rayray2002/TPE-2014/3D/635612493688338750.jpg

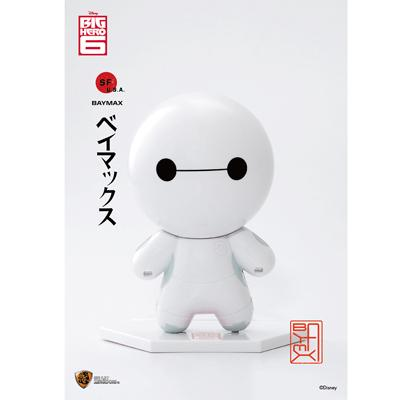
3D/635612493688338750.jpg
