rayray2002/TPE-2014/3D/doggie/images/doggie_front.jpg

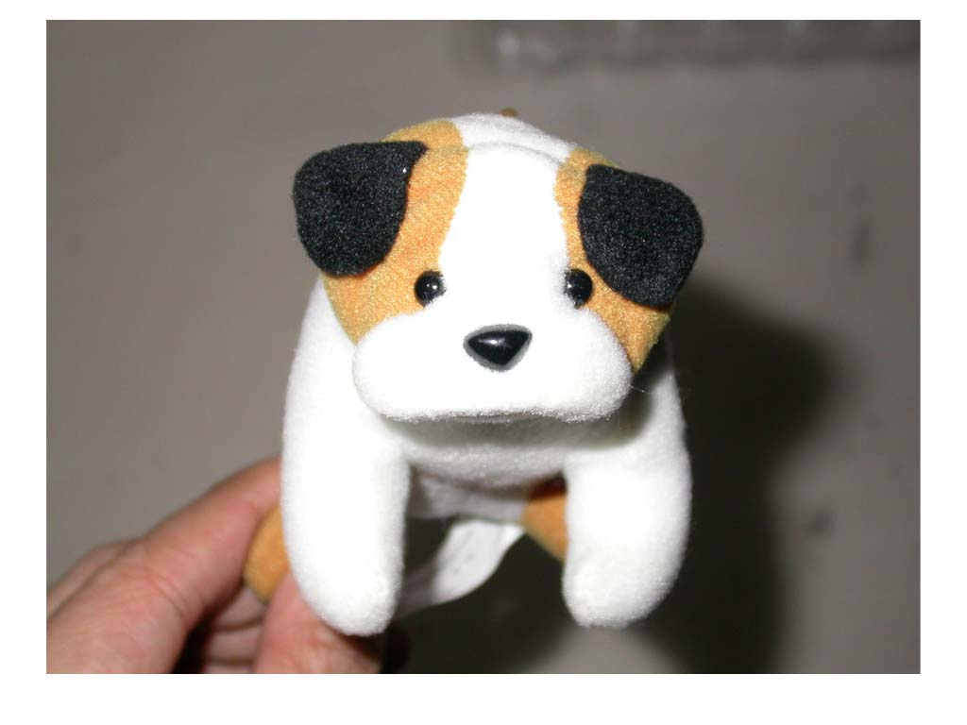
3D/doggie/images/doggie_front.jpg
