rayray2002/TPE-2014/document/Deep Sea Submarine.png

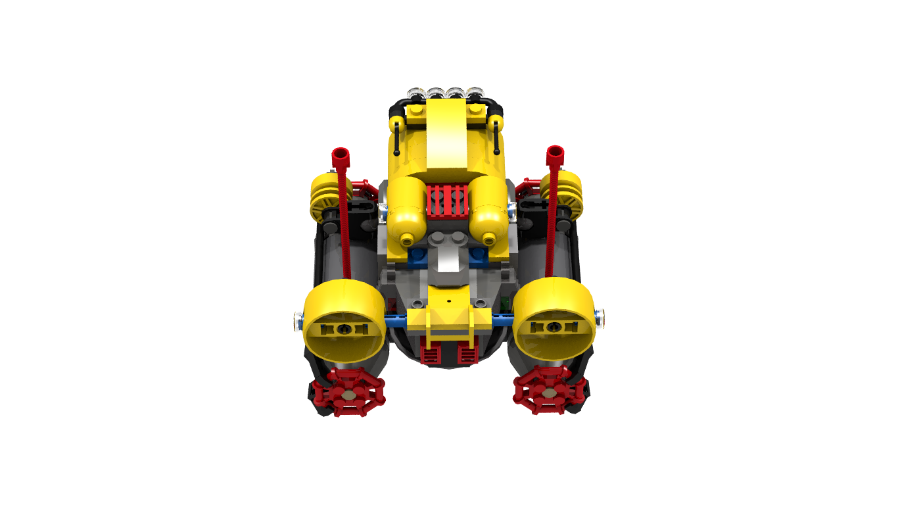
document/Deep Sea Submarine.png
