rayray2002/TPE-2014/document/images/20ms.png

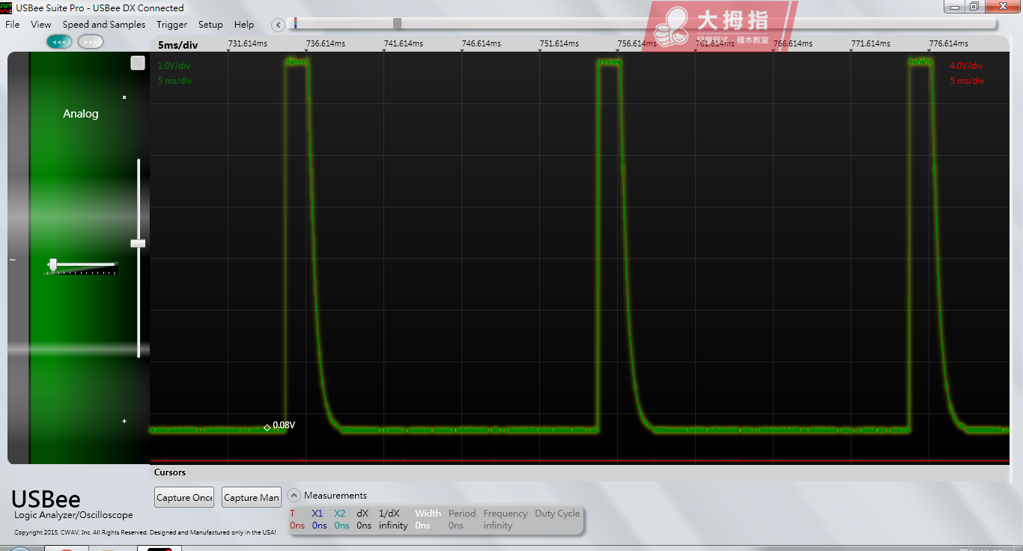
document/images/20ms.png
