rayray2002/TPE-2014/document/images/.picasaoriginals/IMG_7483.JPG

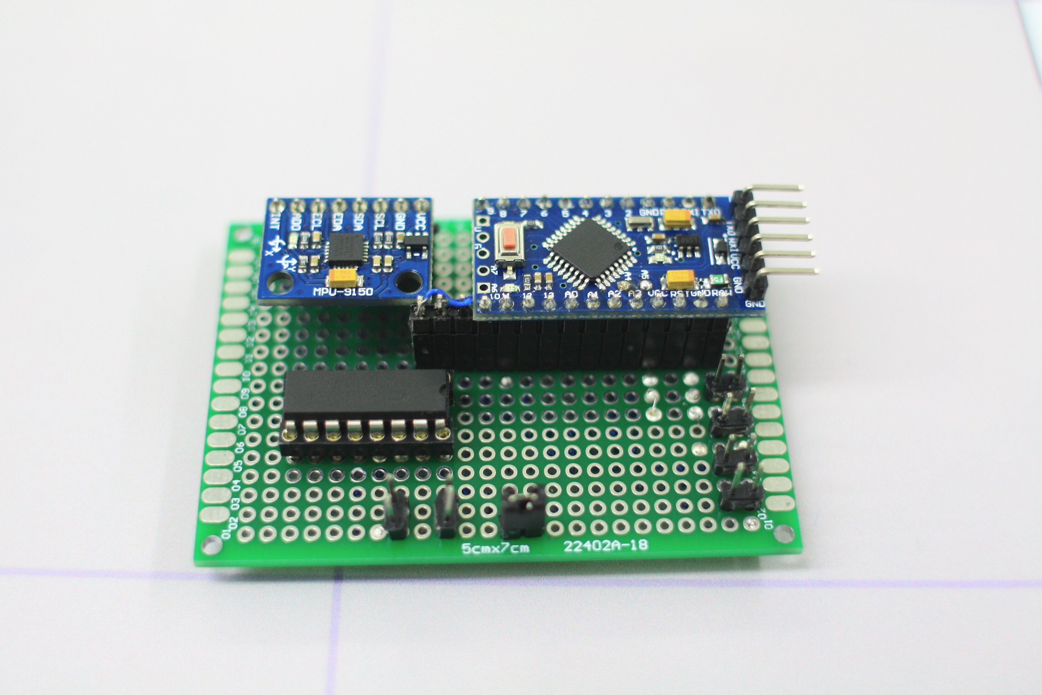
document/images/.picasaoriginals/IMG_7483.JPG
