rayray2002/TPE-2014/document/images/arduino_bb.png

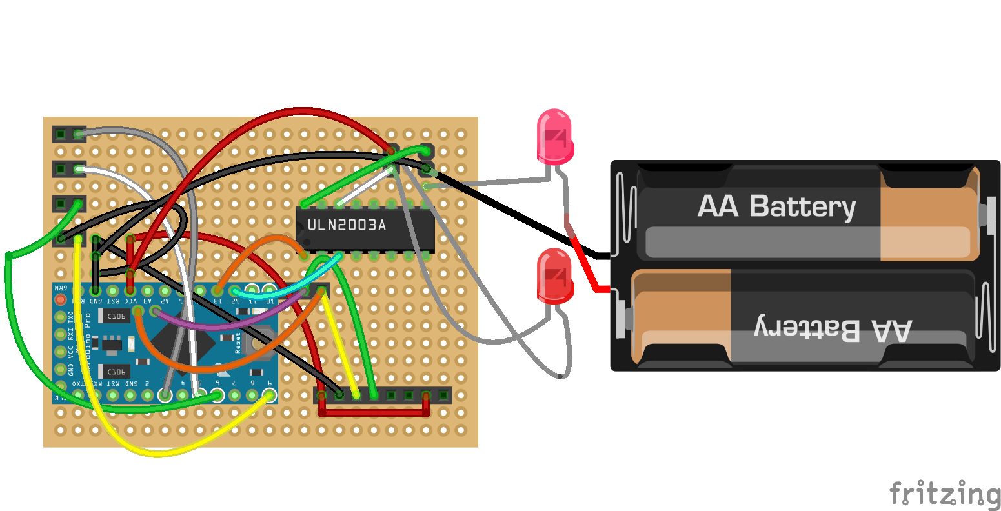
document/images/arduino_bb.png
