rayray2002/TPE-2014/document/images/cdraw (1).png

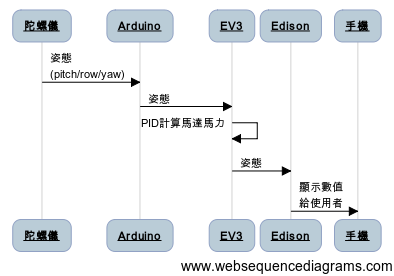
document/images/cdraw (1).png
