rayray2002/TPE-2014/document/images/cdraw.png

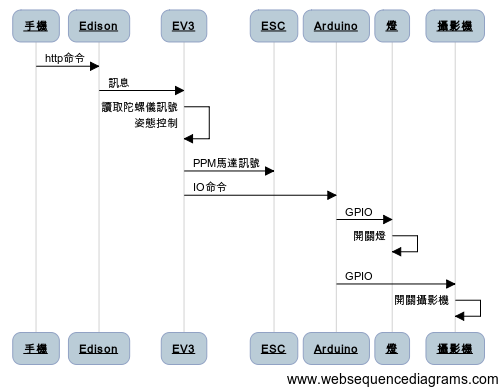
document/images/cdraw.png
