rayray2002/TPE-2014/document/images/IMG_3889.JPG

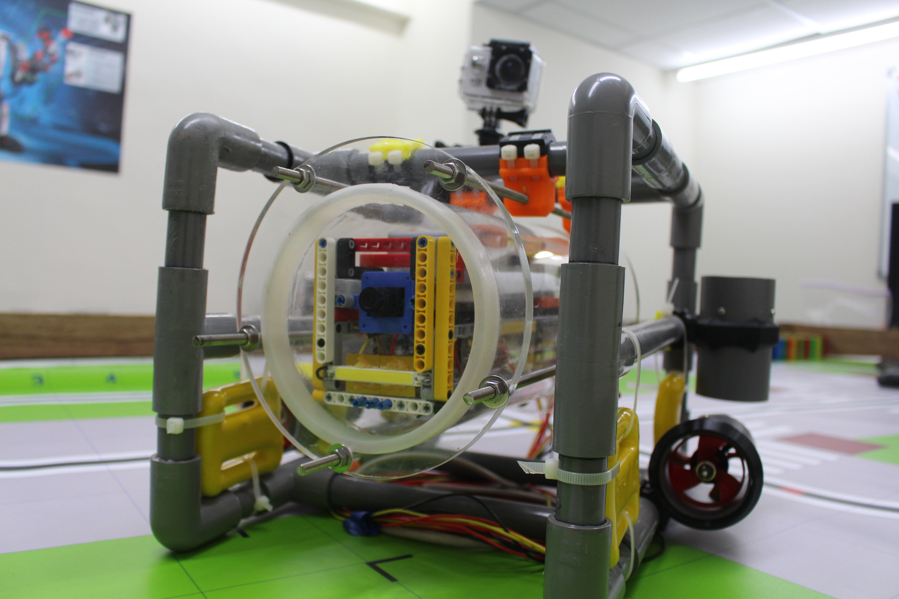
document/images/IMG_3889.JPG
