rayray2002/TPE-2014/document/images/IMG_3899.JPG

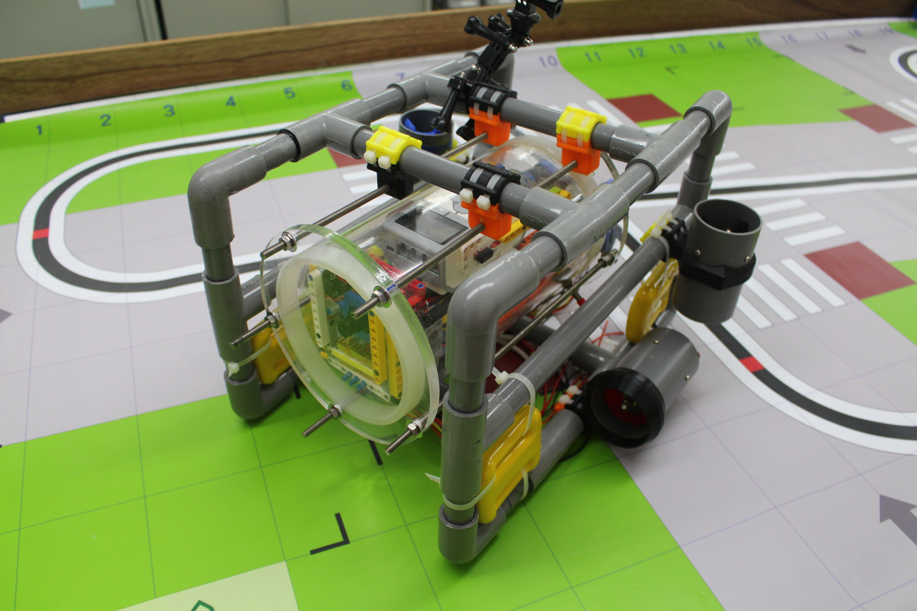
document/images/IMG_3899.JPG
