rayray2002/TPE-2014/document/images/IMG_3903.JPG

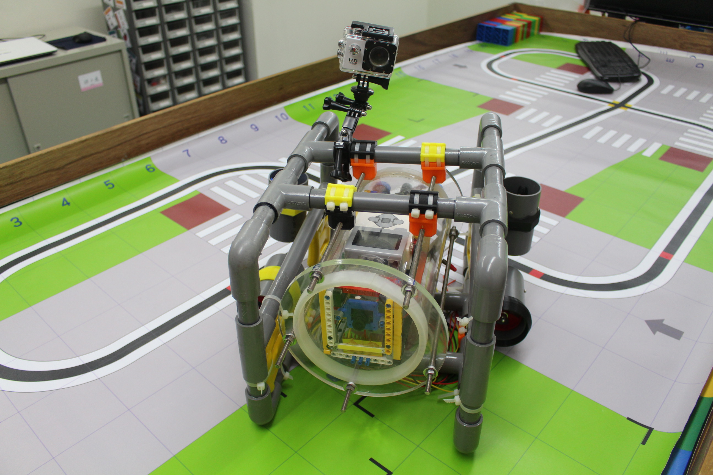
document/images/IMG_3903.JPG
