rayray2002/TPE-2014/document/images/IMG_7483.JPG

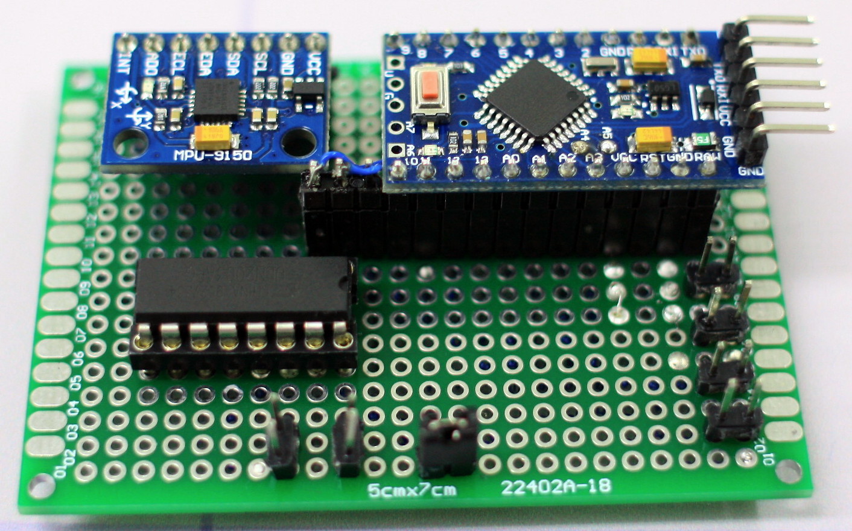
document/images/IMG_7483.JPG
