rayray2002/TPE-2014/document/images/mindmap.png

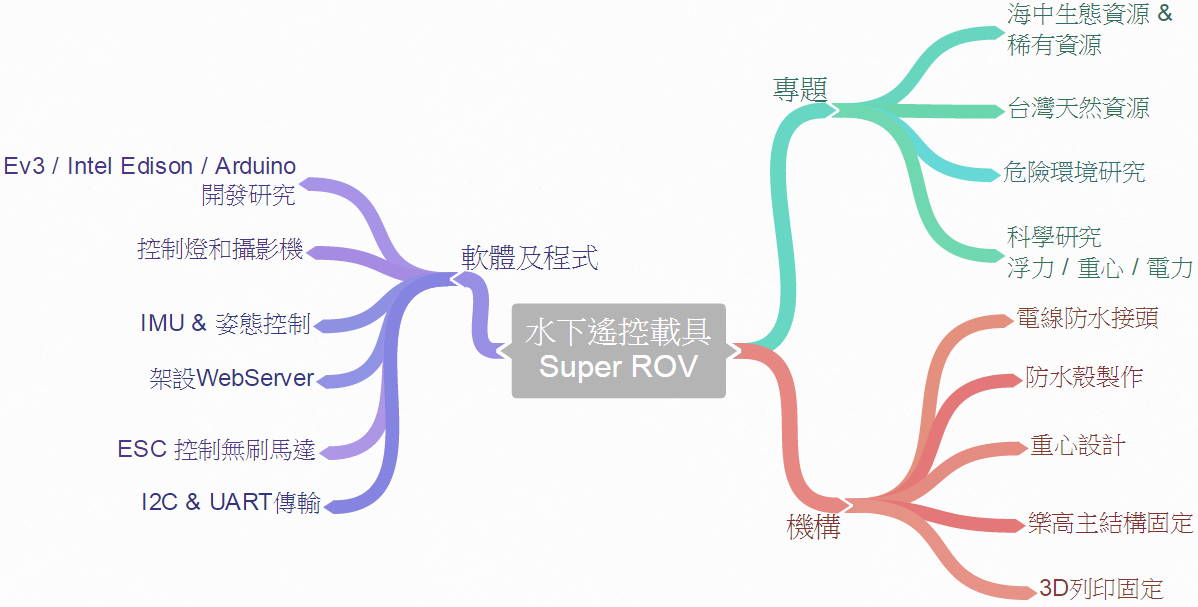
document/images/mindmap.png
