rayray2002/TPE-2014/document/images/pwm.png

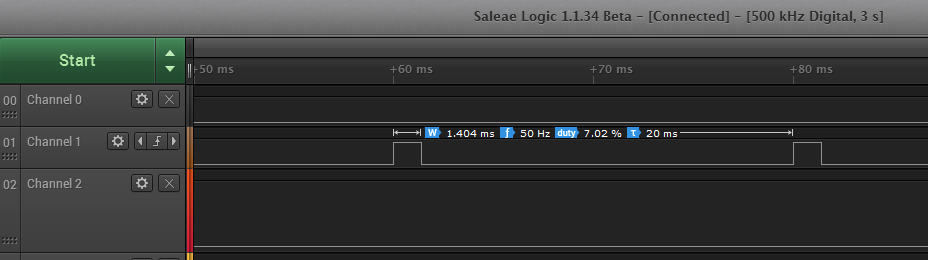
document/images/pwm.png
