rayray2002/TPE-2014/document/images/pwm_in.png

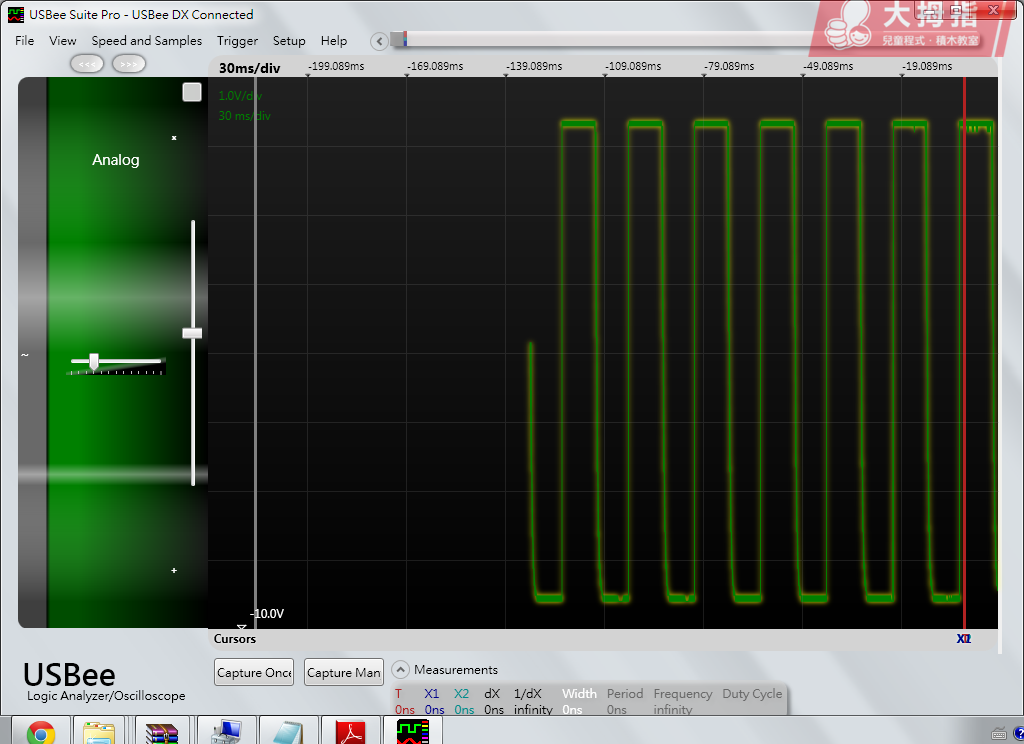
document/images/pwm_in.png
