rayray2002/TPE-2014/edison/images/rov.png

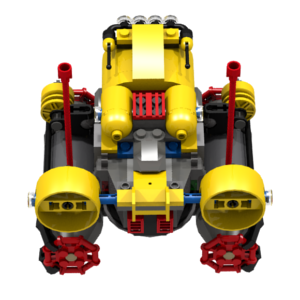
edison/images/rov.png
