rayray2002/TPE-2014/edison/images/ui.png

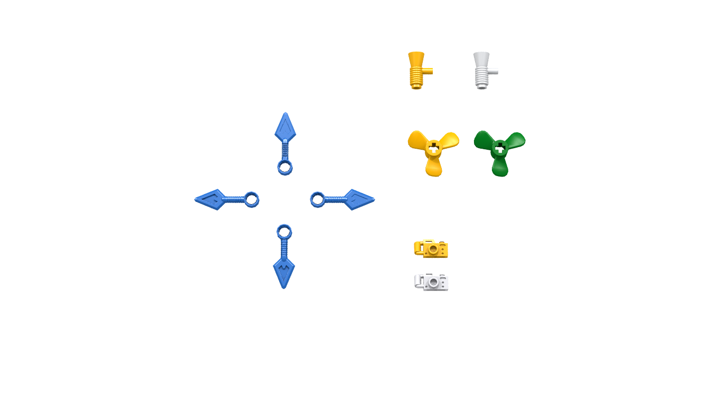
edison/images/ui.png
