rayray2002/TPE-2014/arduino/hc05/hc05.ino

#include <SoftwareSerial.h>

SoftwareSerial mySerial(10, 11); // RX, TX

void setup()
{
  // Open serial communications and wait for port to open:
  Serial.begin(9600);
  while (!Serial) {
    ; // wait for serial port to connect. Needed for Leonardo only
  }


  Serial.println("Goodnight moon2!");

  // set the data rate for the SoftwareSerial port
  mySerial.begin(9600);
  //mySerial.println("Hello, world?");
}

void loop() // run over and over
{
  if (mySerial.available())
    mySerial.write(mySerial.read());
}
